ltebs-polimi/AY2122_II_Project-3/Acquisitions/acquisition_files/acquisitions_for_TEST/3_LETIZIANOLABEL_DRITTO.csv

ACC_X | ACC_Y | ACC_Z | GYR_X | GYR_Y | GYR_Z
1.672 | 0.699 | 1.936 | -229.8 | -20.5 | 247.8
1.672 | 0.699 | 1.936 | -229.8 | -20.5 | 247.8
1.672 | 0.699 | 1.936 | -229.8 | -20.5 | 247.8
1.672 | 0.699 | 1.936 | -229.8 | -20.5 | 247.8
1.672 | 0.699 | 1.936 | -229.8 | -20.5 | 247.8
1.672 | 0.699 | 1.936 | -229.8 | -20.5 | 247.8
1.672 | 0.699 | 1.936 | -229.8 | -20.5 | 247.8
1.672 | 0.699 | 1.936 | -229.8 | -20.5 | 247.8
1.668 | 0.711 | 1.932 | -228.2 | -21.38 | 244.2
1.668 | 0.711 | 1.932 | -228.2 | -21.38 | 244.2
1.672 | 0.699 | 1.936 | -229.8 | -20.5 | 247.8
1.672 | 0.699 | 1.936 | -229.8 | -20.5 | 247.8
1.672 | 0.699 | 1.936 | -229.8 | -20.5 | 247.8
1.672 | 0.699 | 1.936 | -229.8 | -20.5 | 247.8
1.672 | 0.699 | 1.936 | -229.8 | -20.5 | 247.8
1.672 | 0.699 | 1.936 | -229.8 | -20.5 | 247.8
1.672 | 0.699 | 1.936 | -229.8 | -20.5 | 247.8
1.672 | 0.699 | 1.936 | -229.8 | -20.5 | 247.8
1.668 | 0.711 | 1.932 | -228.2 | -21.38 | 244.2
1.668 | 0.711 | 1.932 | -228.2 | -21.38 | 244.2
1.668 | 0.711 | 1.932 | -228.2 | -21.38 | 244.2
1.668 | 0.711 | 1.932 | -228.2 | -21.38 | 244.2
1.668 | 0.711 | 1.932 | -228.2 | -21.38 | 244.2
1.668 | 0.711 | 1.932 | -228.2 | -21.38 | 244.2
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
