ltebs-polimi/AY2122_II_Project-3/Acquisitions/acquisition_files/acquisitions_for_TEST/4_LETIZIANOLABEL_DRITTO.csv

ACC_X | ACC_Y | ACC_Z | GYR_X | GYR_Y | GYR_Z
1.65 | 0.8223 | 1.699 | -170.0 | 31.75 | 135.5
1.65 | 0.8223 | 1.699 | -170.0 | 31.75 | 135.5
1.65 | 0.8223 | 1.699 | -170.0 | 31.75 | 135.5
1.65 | 0.8223 | 1.699 | -170.0 | 31.75 | 135.5
1.65 | 0.8223 | 1.699 | -170.0 | 31.75 | 135.5
1.65 | 0.8223 | 1.699 | -170.0 | 31.75 | 135.5
1.65 | 0.8223 | 1.699 | -170.0 | 31.75 | 135.5
1.641 | 0.869 | 1.699 | -168.0 | 42.0 | 136.2
1.641 | 0.869 | 1.699 | -168.0 | 42.0 | 136.2
1.641 | 0.869 | 1.699 | -168.0 | 42.0 | 136.2
1.65 | 0.8223 | 1.699 | -170.0 | 31.75 | 135.5
1.65 | 0.8223 | 1.699 | -170.0 | 31.75 | 135.5
1.65 | 0.8223 | 1.699 | -170.0 | 31.75 | 135.5
1.65 | 0.8223 | 1.699 | -170.0 | 31.75 | 135.5
1.65 | 0.8223 | 1.699 | -170.0 | 31.75 | 135.5
1.65 | 0.8223 | 1.699 | -170.0 | 31.75 | 135.5
1.65 | 0.8223 | 1.699 | -170.0 | 31.75 | 135.5
1.641 | 0.869 | 1.699 | -168.0 | 42.0 | 136.2
1.641 | 0.869 | 1.699 | -168.0 | 42.0 | 136.2
1.641 | 0.869 | 1.699 | -168.0 | 42.0 | 136.2
-1.865 | 1.52 | 1.822 | 223.2 | 221.2 | 186.8
-1.854 | 1.516 | 1.826 | 221.2 | 224.8 | 190.5
-1.854 | 1.516 | 1.826 | 221.2 | 224.8 | 190.5
-1.854 | 1.516 | 1.826 | 221.2 | 224.8 | 190.5
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
