ltebs-polimi/AY2122_II_Project-3/Acquisitions/acquisition_files/acquisitions_for_TEST/5_LETIZIANOLABEL_DRITTO.csv

ACC_X | ACC_Y | ACC_Z | GYR_X | GYR_Y | GYR_Z
1.805 | 1.334 | 1.91 | -205.5 | 96.25 | 192.8
1.805 | 1.334 | 1.91 | -205.5 | 96.25 | 192.8
1.805 | 1.334 | 1.91 | -205.5 | 96.25 | 192.8
1.805 | 1.334 | 1.91 | -205.5 | 96.25 | 192.8
1.805 | 1.334 | 1.91 | -205.5 | 96.25 | 192.8
1.805 | 1.334 | 1.91 | -205.5 | 96.25 | 192.8
1.8125 | 1.352 | 1.914 | -208.2 | 102.5 | 194.0
1.8125 | 1.352 | 1.914 | -208.2 | 102.5 | 194.0
1.8125 | 1.352 | 1.914 | -208.2 | 102.5 | 194.0
1.8125 | 1.352 | 1.914 | -208.2 | 102.5 | 194.0
1.805 | 1.334 | 1.91 | -205.5 | 96.25 | 192.8
1.805 | 1.334 | 1.91 | -205.5 | 96.25 | 192.8
1.805 | 1.334 | 1.91 | -205.5 | 96.25 | 192.8
1.805 | 1.334 | 1.91 | -205.5 | 96.25 | 192.8
1.805 | 1.334 | 1.91 | -205.5 | 96.25 | 192.8
1.805 | 1.334 | 1.91 | -205.5 | 96.25 | 192.8
1.8125 | 1.352 | 1.914 | -208.2 | 102.5 | 194.0
1.8125 | 1.352 | 1.914 | -208.2 | 102.5 | 194.0
1.8125 | 1.352 | 1.914 | -208.2 | 102.5 | 194.0
1.8125 | 1.352 | 1.914 | -208.2 | 102.5 | 194.0
1.885 | 1.363 | 1.965 | 216.5 | -168.9 | -198.6
1.885 | 1.363 | 1.965 | 216.5 | -168.9 | -198.6
1.885 | 1.363 | 1.965 | 216.5 | -168.9 | -198.6
1.885 | 1.363 | 1.965 | 216.5 | -168.9 | -198.6
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
