ltebs-polimi/AY2122_II_Project-3/Acquisitions/acquisition_files/acquisitions_for_TEST/LETIZIANOLABEL_BATTUTA1.csv

ACC_X | ACC_Y | ACC_Z | GYR_X | GYR_Y | GYR_Z
-1.184 | 1.916 | -1.761 | 195.8 | -77.0 | 192.8
-1.184 | 1.916 | -1.761 | 195.8 | -77.0 | 192.8
-1.184 | 1.916 | -1.761 | 195.8 | -77.0 | 192.8
-1.184 | 1.916 | -1.761 | 195.8 | -77.0 | 192.8
-1.184 | 1.916 | -1.761 | 195.8 | -77.0 | 192.8
-1.184 | 1.916 | -1.761 | 195.8 | -77.0 | 192.8
-1.184 | 1.916 | -1.761 | 195.8 | -77.0 | 192.8
-1.184 | 1.916 | -1.761 | 195.8 | -77.0 | 192.8
-1.184 | 1.916 | -1.761 | 195.8 | -77.0 | 192.8
-1.182 | 1.922 | -1.755 | 193.2 | -78.75 | 193.2
-1.184 | 1.916 | -1.761 | 195.8 | -77.0 | 192.8
-1.184 | 1.916 | -1.761 | 195.8 | -77.0 | 192.8
-1.184 | 1.916 | -1.761 | 195.8 | -77.0 | 192.8
-1.184 | 1.916 | -1.761 | 195.8 | -77.0 | 192.8
-1.184 | 1.916 | -1.761 | 195.8 | -77.0 | 192.8
-1.184 | 1.916 | -1.761 | 195.8 | -77.0 | 192.8
-1.184 | 1.916 | -1.761 | 195.8 | -77.0 | 192.8
-1.184 | 1.916 | -1.761 | 195.8 | -77.0 | 192.8
-1.184 | 1.916 | -1.761 | 195.8 | -77.0 | 192.8
-1.182 | 1.922 | -1.755 | 193.2 | -78.75 | 193.2
-1.736 | 1.76 | -0.9736 | 237.2 | -207.1 | 203.0
-1.737 | 1.771 | -0.962 | 237.2 | -207.1 | 203.0
-1.737 | 1.771 | -0.962 | 237.2 | -207.1 | 203.0
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
